ELEC70142-VLSI-Coursework/vlsi_test_platform/gw/src/uart_tx_from_fifo.sv

`timescale 1ns/1ps

module uart_tx_from_fifo (
    input  logic       clk,
    input  logic       rst_n,

    // -------- Reply FIFO interface --------
    input  logic       fifo_empty,
    output logic       fifo_rd_en,
    input  logic [7:0] fifo_rd_data,

    // -------- UART TX interface --------
    output logic [7:0] tx_data,
    output logic       tx_valid,
    input  logic       tx_ready
);


    assign tx_data = fifo_rd_data;
    // ---------------------------------------------------------
    // Control logic
    // ---------------------------------------------------------
    always_ff @(posedge clk) begin
        if (!rst_n) begin
            fifo_rd_en <= 1'b0;
            tx_valid   <= 1'b0;
        end
        else begin
            fifo_rd_en <= 1'b0;
            tx_valid   <= 1'b0;

            // If UART is ready and FIFO has data, transmit next byte
            if (tx_ready && !fifo_empty) begin
                fifo_rd_en <= 1'b1;    // pop FIFO
                tx_valid   <= 1'b1;    // start UART TX
                // tx_data is driven combinationally from fifo_rd_data
            end
        end
    end

endmodule
